letelescope/ascom-flat-panel/drivers/ASCOM/ASCOM_7_Driver/WizardImage.bmp

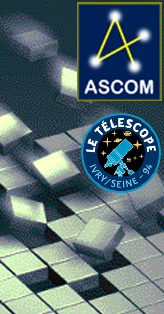
drivers/ASCOM/ASCOM_7_Driver/WizardImage.bmp
